Scorpion9000IQmech/Spotify-Display/Spotify Display connections for componets.kicad_sch

## KiCad design Spotify Display connections for componets.kicad_sch (2026-06-22)

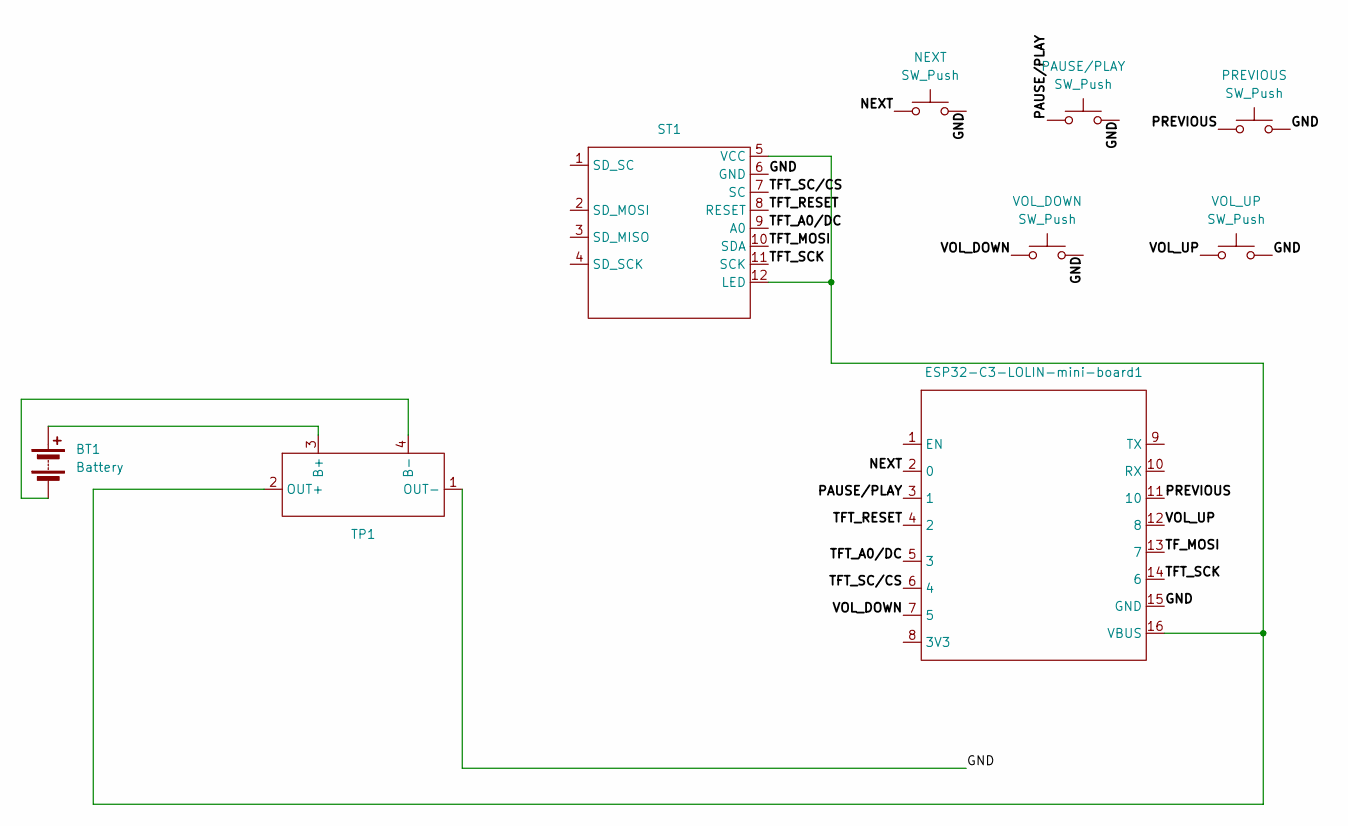
[picture p3: schematic Spotify Display connections for componets.kicad_sch]

Parts:
BT1: Battery
ESP32-C3-LOLIN-mini-board1: (no value)
NEXT: SW_Push
PAUSE/PLAY: SW_Push
PREVIOUS: SW_Push
ST1: (no value)
TP1: (no value)
VOL_DOWN: SW_Push
VOL_UP: SW_Push

Connections:
GND: ESP32-C3-LOLIN-mini-board1.15 (GND), NEXT.2, PAUSE/PLAY.2, PREVIOUS.2, ST1.6 (GND), TP1.1 (OUT-), VOL_DOWN.2, VOL_UP.2
NEXT: ESP32-C3-LOLIN-mini-board1.2 (0), NEXT.1
unnamed: BT1.1 (+), TP1.3 (B+)
unnamed: BT1.2 (-), TP1.4 (B-)
unnamed: ESP32-C3-LOLIN-mini-board1.16 (VBUS), ST1.5 (VCC), ST1.12 (LED), TP1.2 (OUT+)
PAUSE/PLAY: ESP32-C3-LOLIN-mini-board1.3 (1), PAUSE/PLAY.1
PREVIOUS: ESP32-C3-LOLIN-mini-board1.11 (10), PREVIOUS.1
TFT_A0/DC: ESP32-C3-LOLIN-mini-board1.5 (3), ST1.9 (A0)
TFT_MOSI: ST1.10 (SDA)
TFT_RESET: ESP32-C3-LOLIN-mini-board1.4 (2), ST1.8 (RESET)
TFT_SCK: ESP32-C3-LOLIN-mini-board1.14 (6), ST1.11 (SCK)
TFT_SC/CS: ESP32-C3-LOLIN-mini-board1.6 (4), ST1.7 (SC)
TF_MOSI: ESP32-C3-LOLIN-mini-board1.13 (7)
VOL_DOWN: ESP32-C3-LOLIN-mini-board1.7 (5), VOL_DOWN.1
VOL_UP: ESP32-C3-LOLIN-mini-board1.12 (8), VOL_UP.1
